inakiizcue/grantareprap/3DModels/Turbofan/Low_Bypass_Turbofan_Jet_Engine/turbine_section/turbine section/LP turbine case.STL

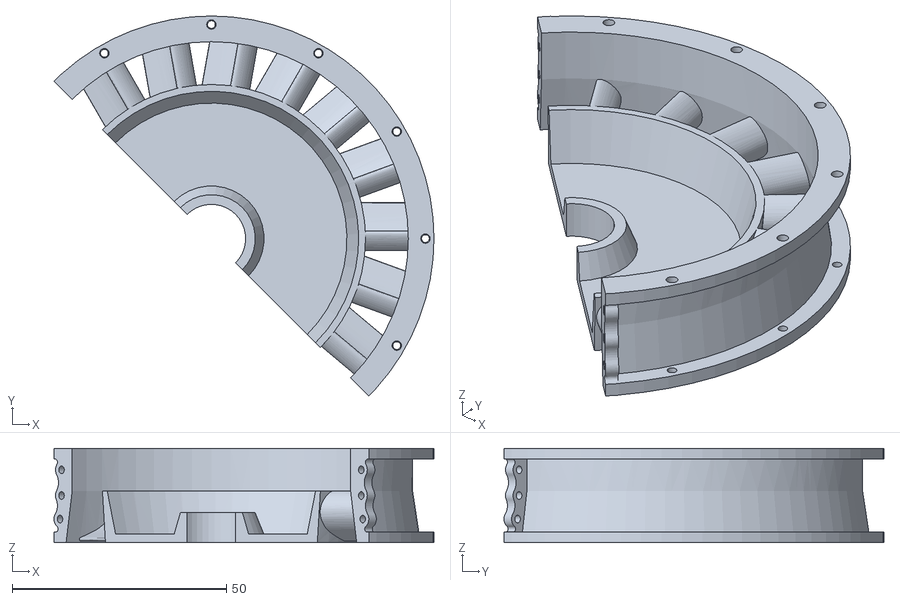
[picture p17: CAD file, 2014-08-12]
3DModels/Turbofan/Low_Bypass_Turbofan_Jet_Engine/turbine_section/turbine section/LP turbine case.STL
88.8 x 88.8 x 22.0
