inakiizcue/grantareprap/3DModels/PL2Q_Hugin/request_PL2Q_Hugin_motormount_no_mouse.stl

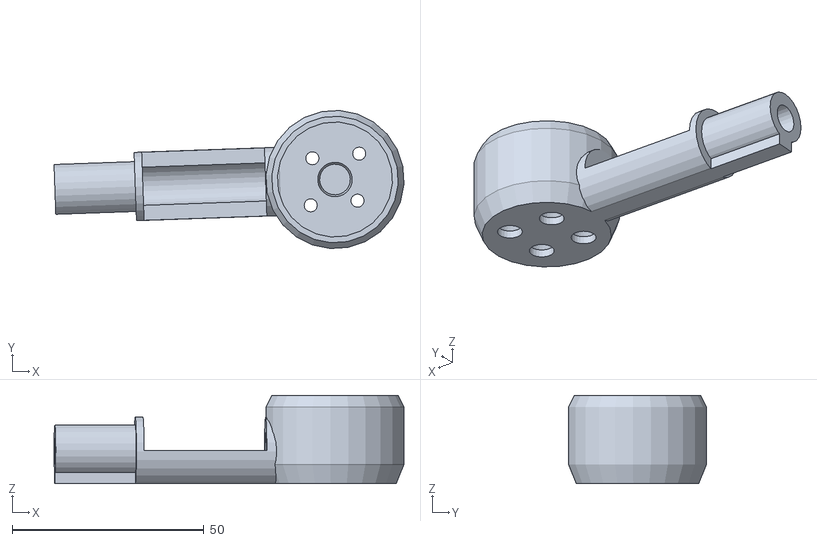
[picture p18: CAD file, 2014-12-12]
3DModels/PL2Q_Hugin/request_PL2Q_Hugin_motormount_no_mouse.stl
91.2 x 36.0 x 23.0
