inakiizcue/grantareprap/3DModels/Print_Bed_Level_Check/LevelRep-20.stl

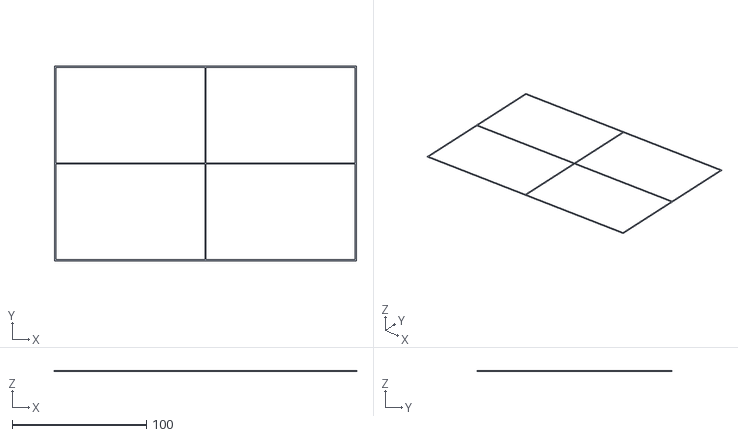
[picture p19: CAD file, 2014-01-20]
3DModels/Print_Bed_Level_Check/LevelRep-20.stl
225.0 x 145.0 x 0.2
