inakiizcue/grantareprap/3DModels/Turbofan/Low_Bypass_Turbofan_Jet_Engine/compressor case/s2.STL

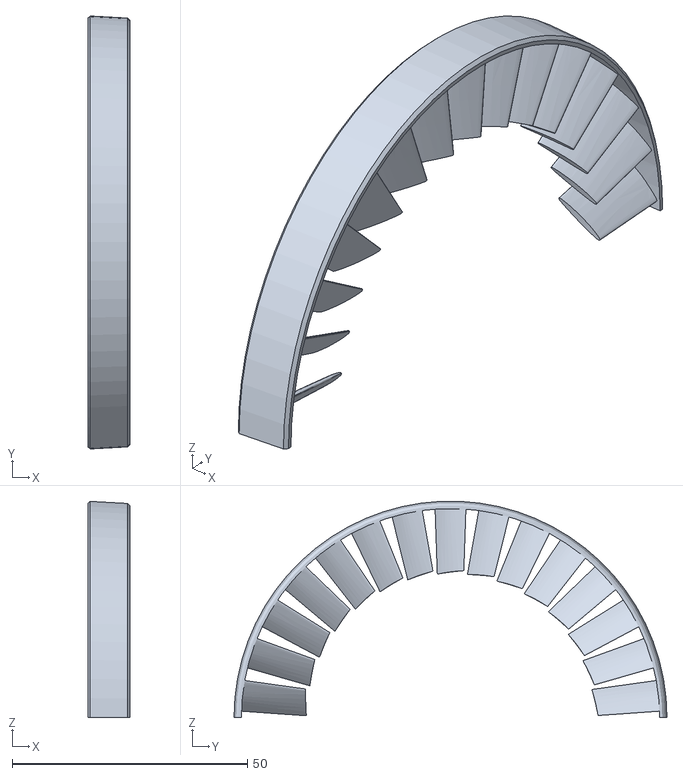
[picture p20: CAD file, 2014-08-12]
3DModels/Turbofan/Low_Bypass_Turbofan_Jet_Engine/compressor case/s2.STL
9.00 x 91.9 x 45.9
