inakiizcue/grantareprap/3DModels/Turbofan/Low_Bypass_Turbofan_Jet_Engine/HP rotor/R5.STL

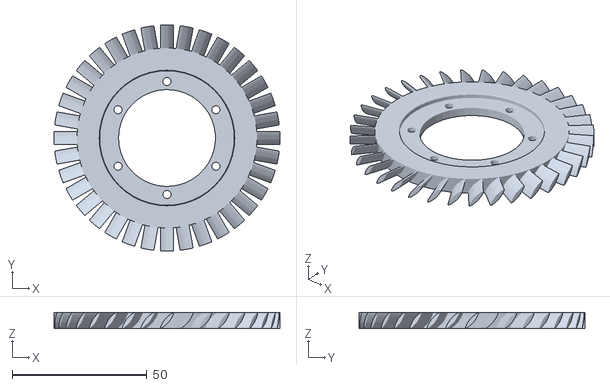
[picture p21: CAD file, 2014-08-12]
3DModels/Turbofan/Low_Bypass_Turbofan_Jet_Engine/HP rotor/R5.STL
84.0 x 84.0 x 6.00
