inakiizcue/grantareprap/3DModels/Turbofan/Low_Bypass_Turbofan_Jet_Engine/Rev_1/scritta.STL

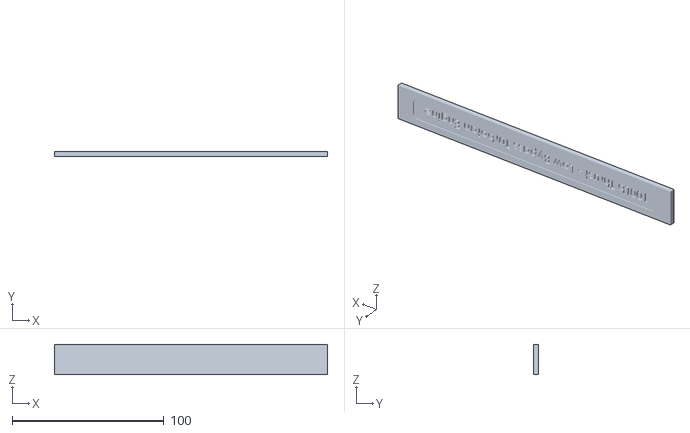
[picture p22: CAD file, 2014-08-12]
3DModels/Turbofan/Low_Bypass_Turbofan_Jet_Engine/Rev_1/scritta.STL
180.0 x 3.00 x 20.0
