inakiizcue/grantareprap/3DModels/PL2Q_Hugin/PL2Q_Hugin_gopro_mount.stl

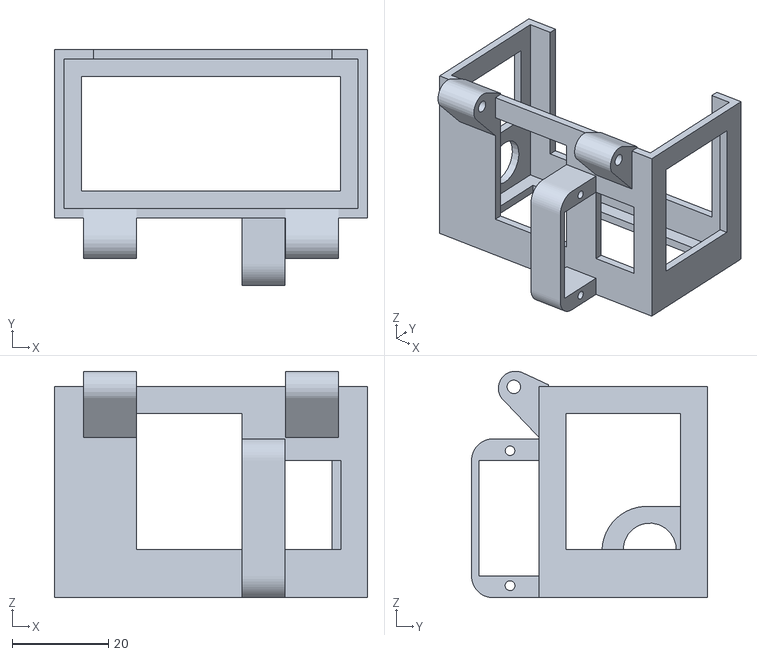
[picture p23: CAD file, 2014-12-12]
3DModels/PL2Q_Hugin/PL2Q_Hugin_gopro_mount.stl
65.0 x 49.0 x 47.0
