inakiizcue/grantareprap/3DModels/Turbofan/Low_Bypass_Turbofan_Jet_Engine/compressor case/S1.STL

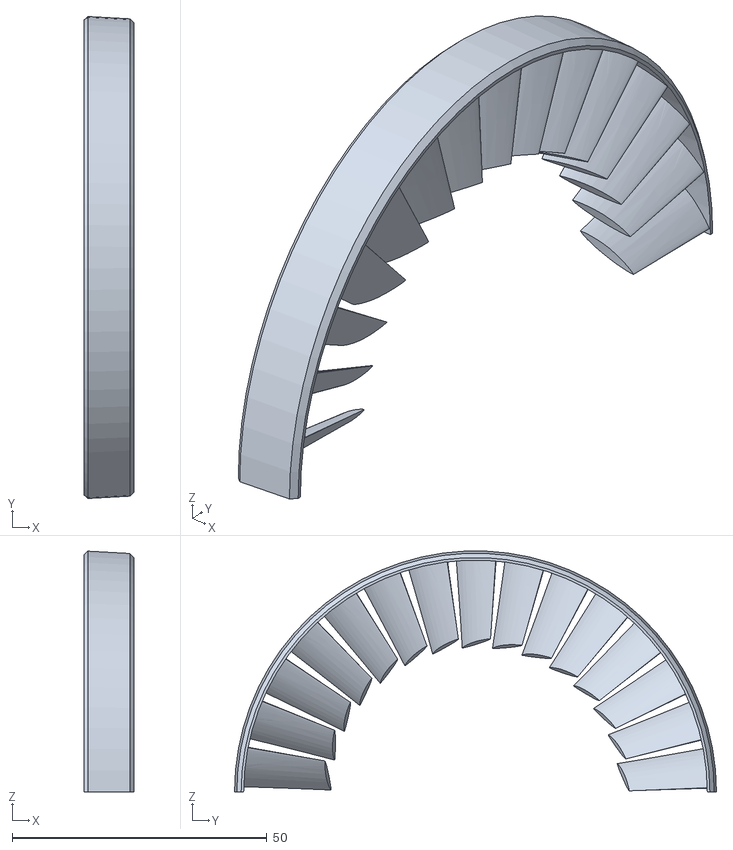
[picture p24: CAD file, 2014-08-12]
3DModels/Turbofan/Low_Bypass_Turbofan_Jet_Engine/compressor case/S1.STL
9.90 x 94.5 x 47.2
