inakiizcue/grantareprap/3DModels/Turbofan/Low_Bypass_Turbofan_Jet_Engine/HP rotor/R4.STL

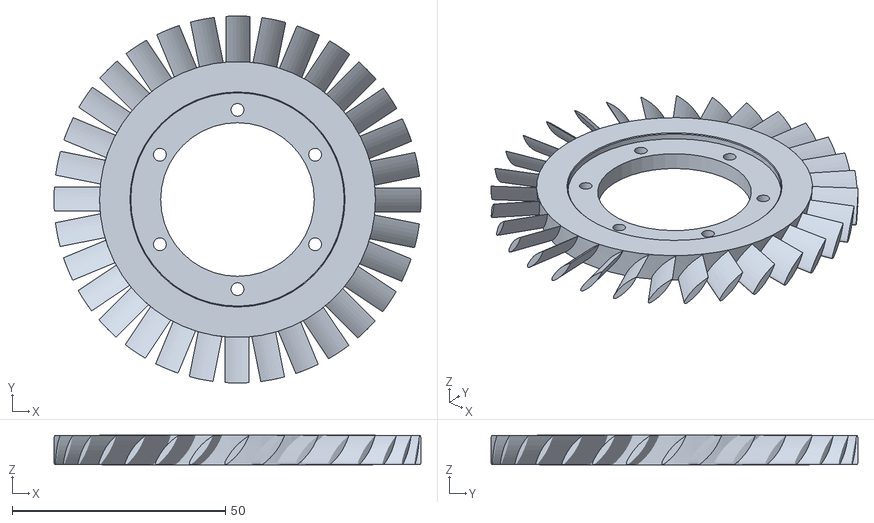
[picture p25: CAD file, 2014-08-12]
3DModels/Turbofan/Low_Bypass_Turbofan_Jet_Engine/HP rotor/R4.STL
86.0 x 86.0 x 7.00
