inakiizcue/grantareprap/3DModels/Turbofan/Low_Bypass_Turbofan_Jet_Engine/Rev_1/stand.STL

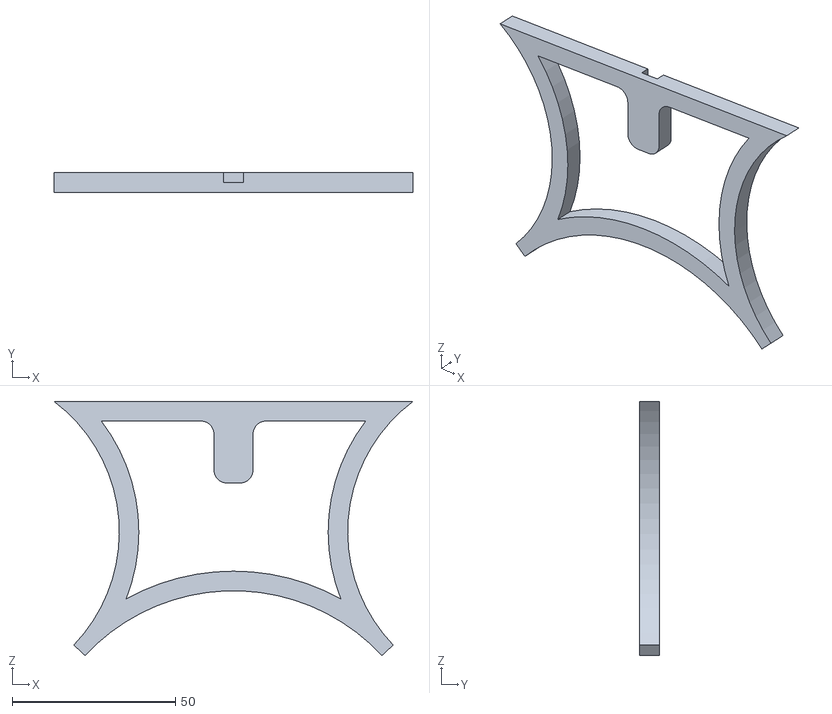
[picture p26: CAD file, 2014-08-12]
3DModels/Turbofan/Low_Bypass_Turbofan_Jet_Engine/Rev_1/stand.STL
110.0 x 6.00 x 77.9
