inakiizcue/grantareprap/3DModels/PL2Q_Hugin/PL2Q_Hugin_canopy.stl

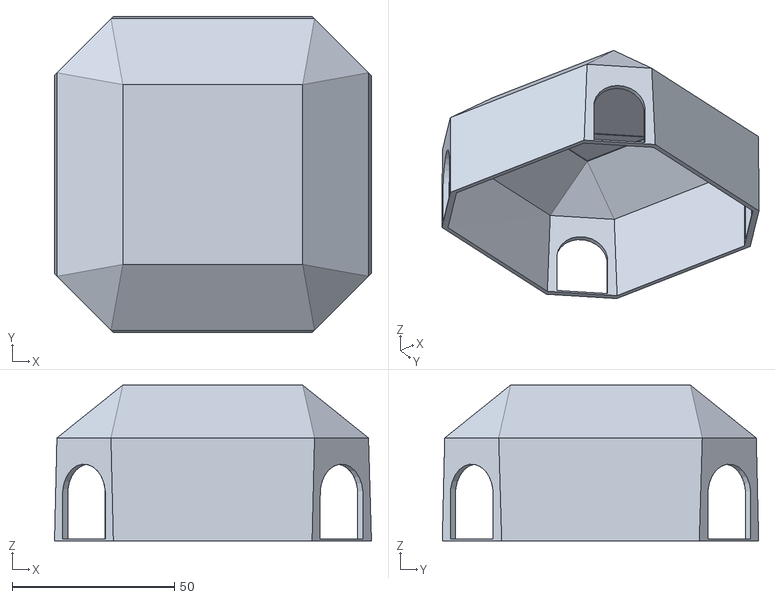
[picture p27: CAD file, 2014-12-12]
3DModels/PL2Q_Hugin/PL2Q_Hugin_canopy.stl
97.7 x 97.6 x 48.1
