inakiizcue/grantareprap/3DModels/Turbofan/Low_Bypass_Turbofan_Jet_Engine/compressor case/S4.STL

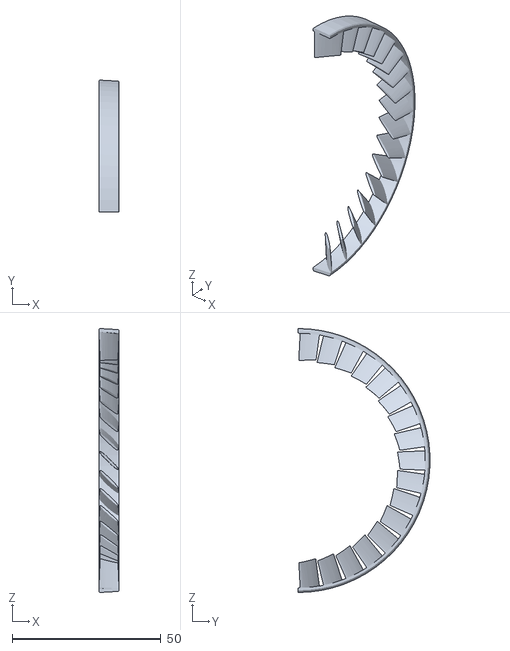
[picture p28: CAD file, 2014-08-12]
3DModels/Turbofan/Low_Bypass_Turbofan_Jet_Engine/compressor case/S4.STL
6.80 x 44.3 x 88.8
