inakiizcue/grantareprap/3DModels/Turbofan/Low_Bypass_Turbofan_Jet_Engine/HP rotor/R4Spacer.STL

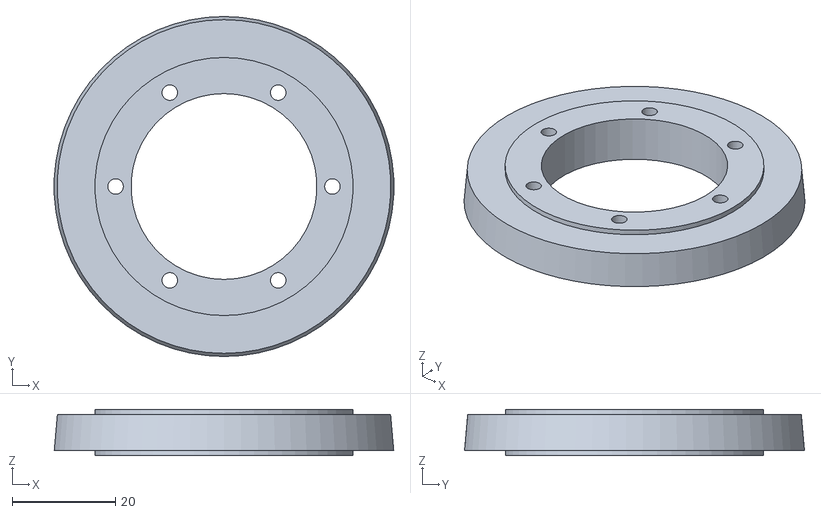
[picture p29: CAD file, 2014-08-12]
3DModels/Turbofan/Low_Bypass_Turbofan_Jet_Engine/HP rotor/R4Spacer.STL
65.8 x 65.9 x 9.00
