inakiizcue/grantareprap/3DModels/PL2Q_Hugin/PL2Q_Hugin_arm.stl

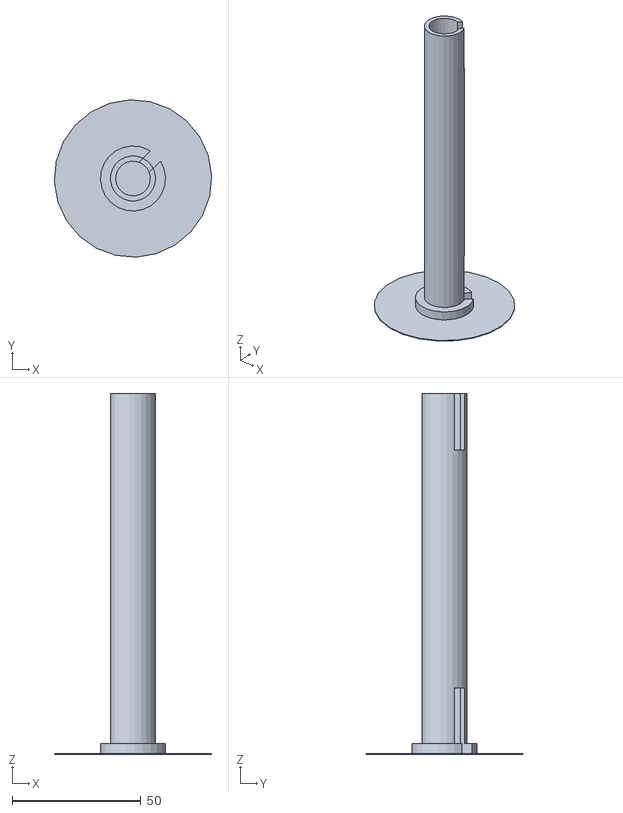
[picture p30: CAD file, 2014-12-12]
3DModels/PL2Q_Hugin/PL2Q_Hugin_arm.stl
61.2 x 61.2 x 140.3
