inakiizcue/grantareprap/3DModels/Turbofan/Low_Bypass_Turbofan_Jet_Engine/compressor case/S3.STL

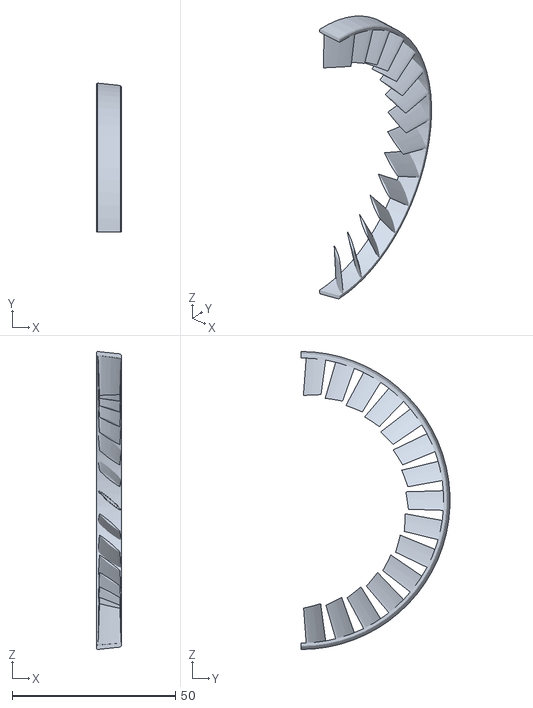
[picture p31: CAD file, 2014-08-12]
3DModels/Turbofan/Low_Bypass_Turbofan_Jet_Engine/compressor case/S3.STL
7.60 x 45.5 x 91.1
