inakiizcue/grantareprap/3DModels/Turbofan/Low_Bypass_Turbofan_Jet_Engine/HP rotor/R1Spacer.STL

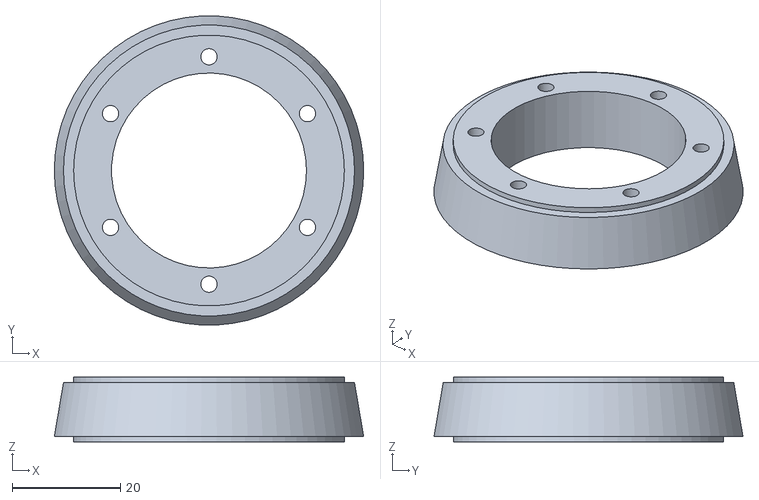
[picture p32: CAD file, 2014-08-12]
3DModels/Turbofan/Low_Bypass_Turbofan_Jet_Engine/HP rotor/R1Spacer.STL
57.1 x 57.1 x 12.0
