inakiizcue/grantareprap/3DModels/PL2Q_Hugin/PL2Q_Hugin_cam_holder.stl

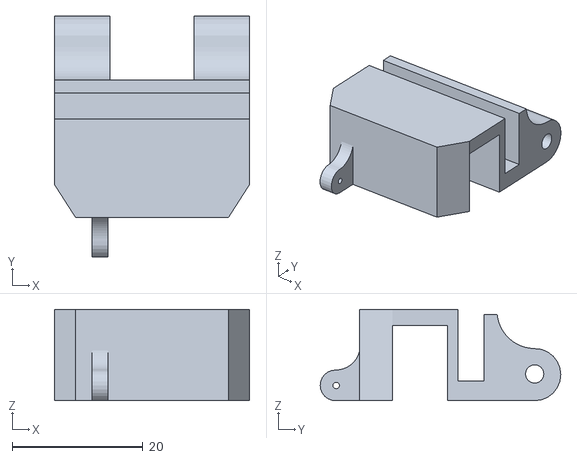
[picture p33: CAD file, 2014-12-12]
3DModels/PL2Q_Hugin/PL2Q_Hugin_cam_holder.stl
29.9 x 36.8 x 14.0
