inakiizcue/grantareprap/3DModels/Turbofan/Low_Bypass_Turbofan_Jet_Engine/compressor case/CC Diffuser 2.STL

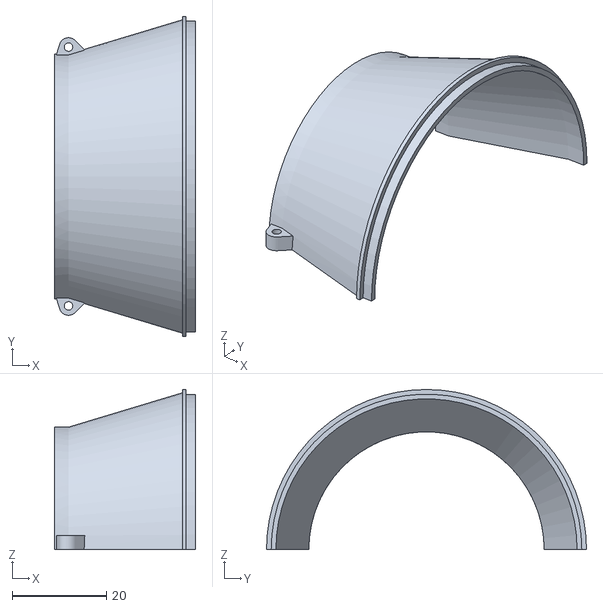
[picture p34: CAD file, 2014-08-12]
3DModels/Turbofan/Low_Bypass_Turbofan_Jet_Engine/compressor case/CC Diffuser 2.STL
30.0 x 68.0 x 34.0
