inakiizcue/grantareprap/3DModels/Turbofan/Low_Bypass_Turbofan_Jet_Engine/HP rotor/R5Spacer.STL

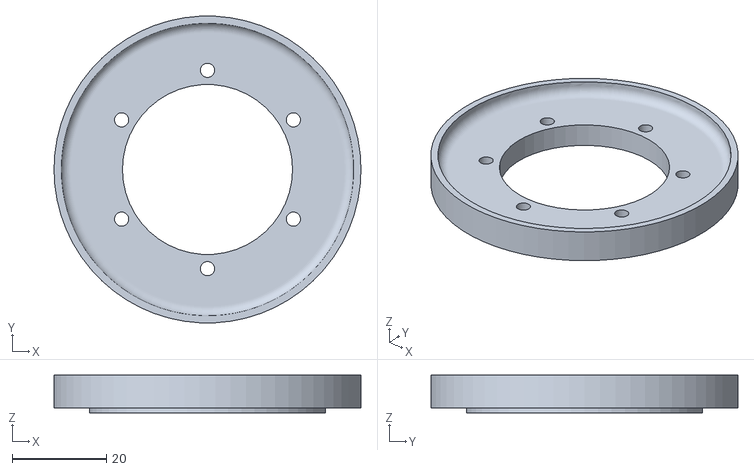
[picture p35: CAD file, 2014-08-12]
3DModels/Turbofan/Low_Bypass_Turbofan_Jet_Engine/HP rotor/R5Spacer.STL
65.0 x 64.9 x 8.00
