inakiizcue/grantareprap/3DModels/PL2Q_Hugin/request_PL2Q_Hugin_body_no_mouse.stl

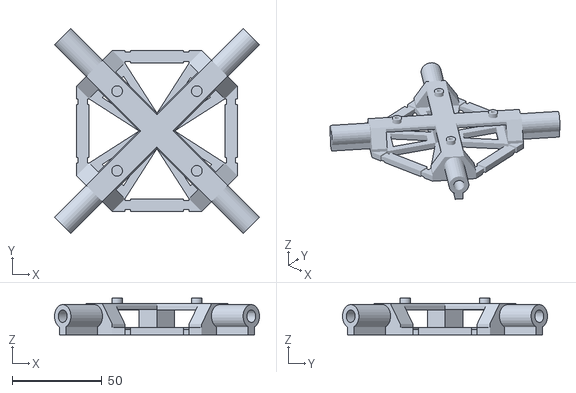
[picture p36: CAD file, 2014-12-12]
3DModels/PL2Q_Hugin/request_PL2Q_Hugin_body_no_mouse.stl
114.5 x 114.5 x 20.5
