inakiizcue/grantareprap/3DModels/PL2Q_Hugin/request_PL2Q_Hugin_arm_no_base_raft.stl

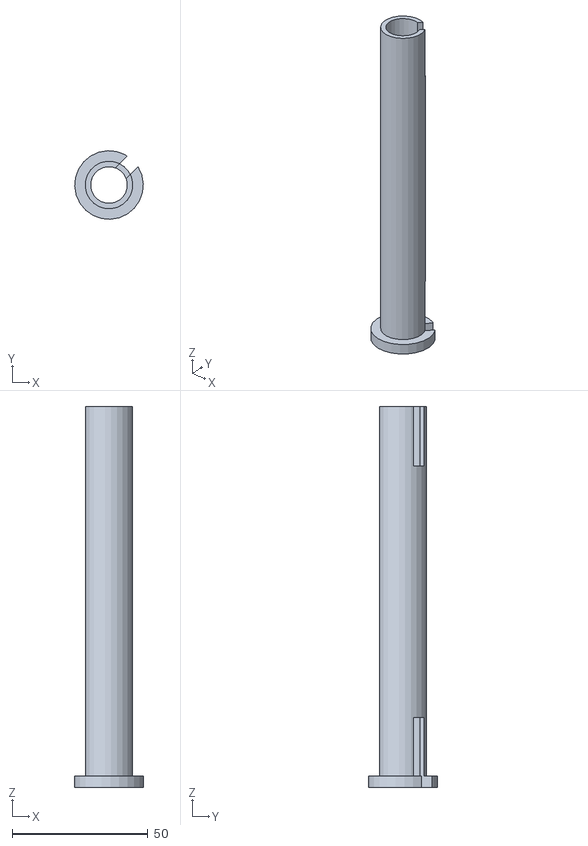
[picture p38: CAD file, 2014-12-12]
3DModels/PL2Q_Hugin/request_PL2Q_Hugin_arm_no_base_raft.stl
25.3 x 25.3 x 140.3
