inakiizcue/grantareprap/3DModels/PL2Q_Hugin/update_PL2Q_Hugin_arm_x4.stl

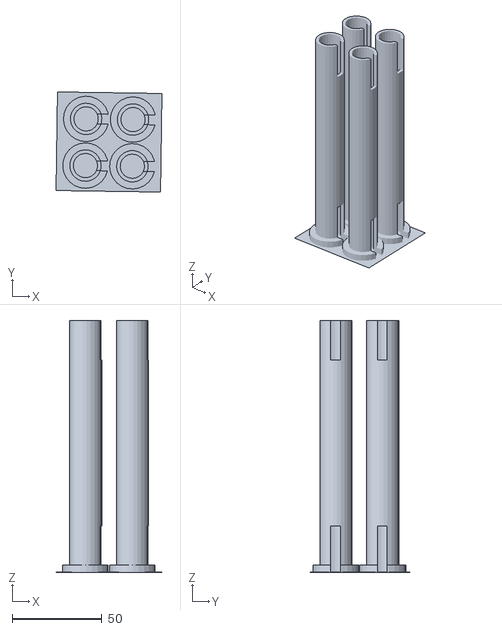
[picture p39: CAD file, 2014-12-12]
3DModels/PL2Q_Hugin/update_PL2Q_Hugin_arm_x4.stl
59.0 x 55.7 x 140.3
