inakiizcue/grantareprap/3DModels/PL2Q_Hugin/PL2Q_Hugin_gopro_legs.stl

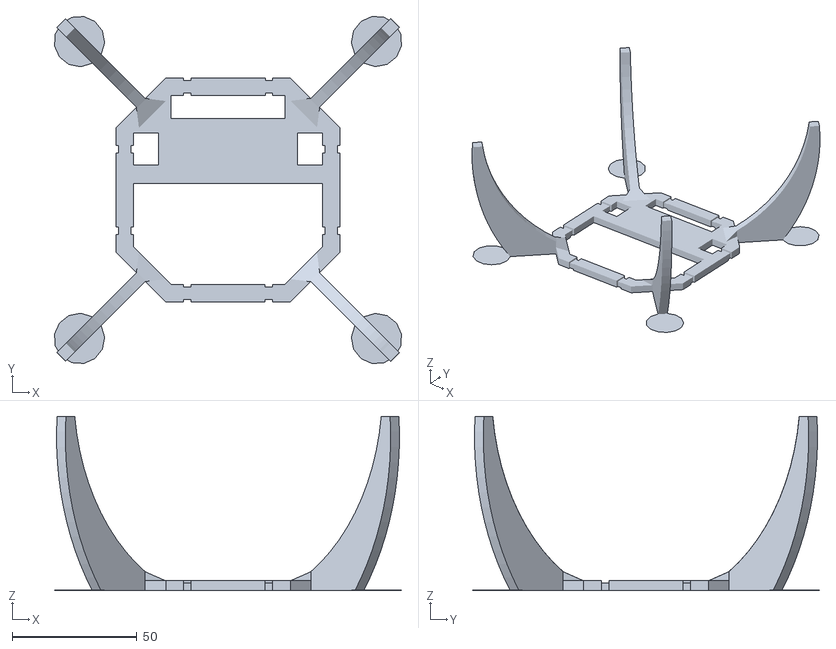
[picture p40: CAD file, 2014-12-12]
3DModels/PL2Q_Hugin/PL2Q_Hugin_gopro_legs.stl
139.3 x 139.3 x 70.0
