inakiizcue/grantareprap/3DModels/PL2Q_Hugin/PL2Q_Hugin_motormount.stl

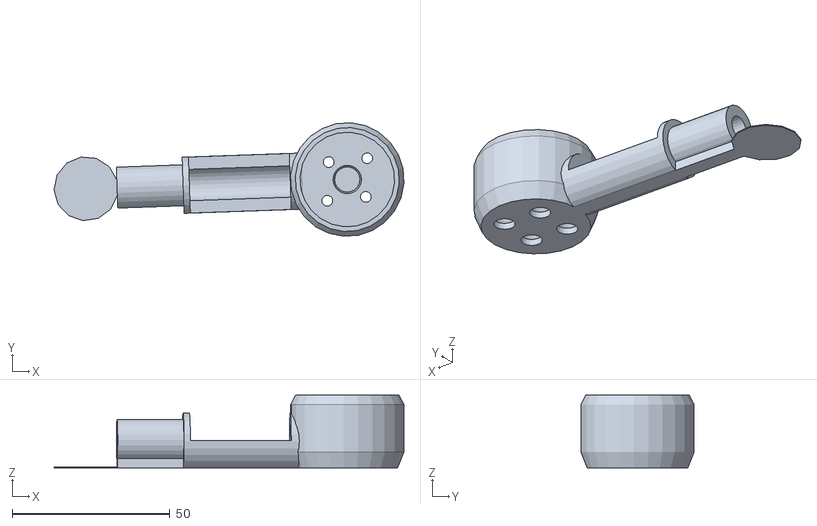
[picture p41: CAD file, 2014-12-12]
3DModels/PL2Q_Hugin/PL2Q_Hugin_motormount.stl
111.0 x 36.0 x 23.0
