inakiizcue/grantareprap/3DModels/PL2Q_Hugin/PL2Q_Hugin_receiver_canopy.stl

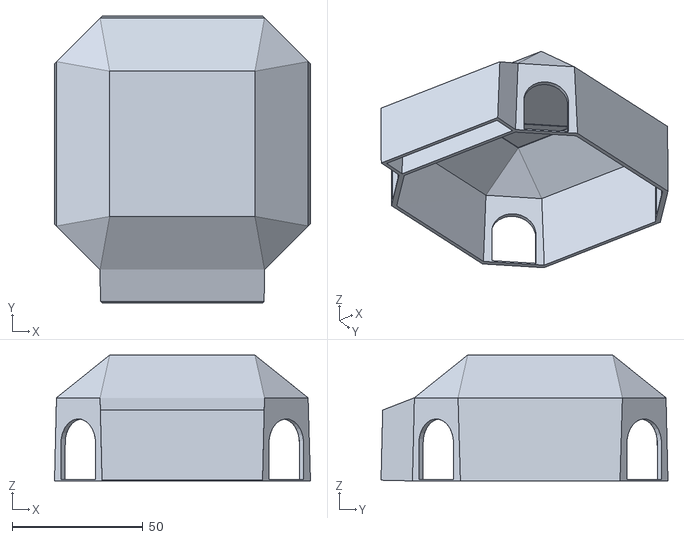
[picture p42: CAD file, 2014-12-12]
3DModels/PL2Q_Hugin/PL2Q_Hugin_receiver_canopy.stl
97.7 x 109.6 x 48.1
